jeffqchen/PS2EasyHDD/GameStar/3D Printing/Outer Shell & Tray Cover/Thin/Inner Tray Cover 9.5mm.stl

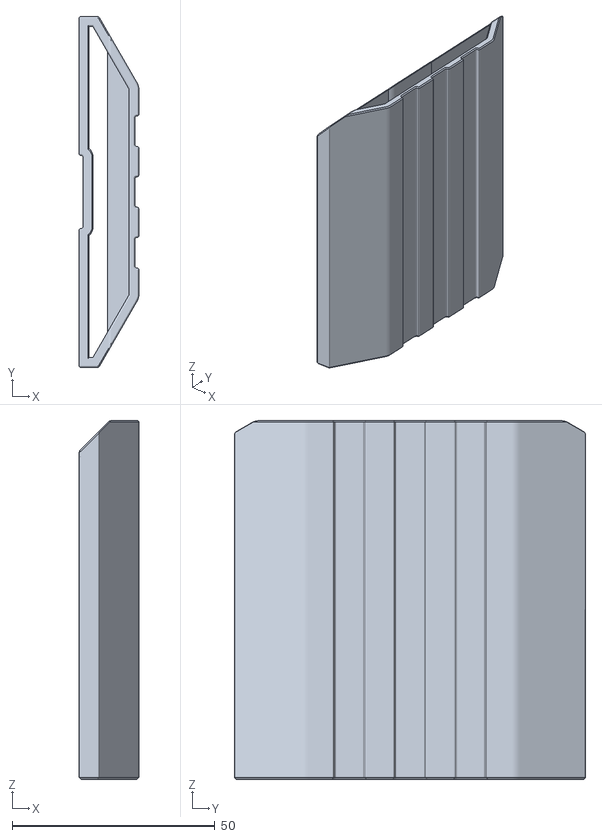
[picture p17: CAD file, 2024-02-22]
GameStar/3D Printing/Outer Shell & Tray Cover/Thin/Inner Tray Cover 9.5mm.stl
14.8 x 86.6 x 88.6
