jeffqchen/PS2EasyHDD/SCPH-10281/3D Printing/Inner Tray Short.stl

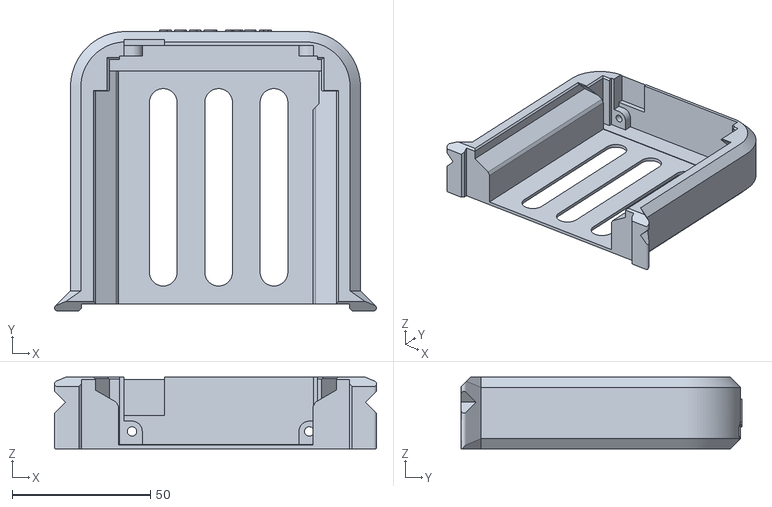
[picture p18: CAD file, 2024-02-20]
SCPH-10281/3D Printing/Inner Tray Short.stl
116.3 x 101.4 x 26.0
