jeffqchen/PS2EasyHDD/SCPH-10281/3D Printing/Outer Shell & Tray Cover/Inner Tray Cover 7mm.stl

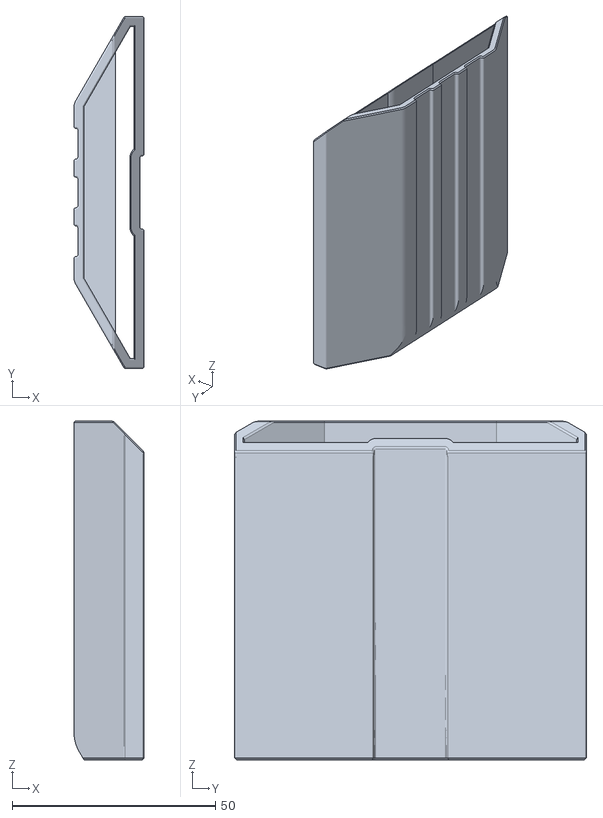
[picture p19: CAD file, 2024-02-18]
SCPH-10281/3D Printing/Outer Shell & Tray Cover/Inner Tray Cover 7mm.stl
17.3 x 86.6 x 83.4
