jeffqchen/PS2EasyHDD/GameStar/3D Printing/Inner Tray Short.stl

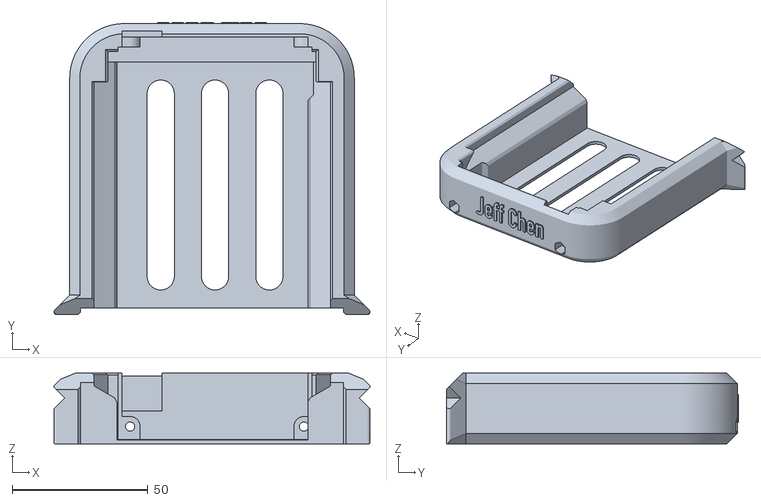
[picture p20: CAD file, 2024-02-22]
GameStar/3D Printing/Inner Tray Short.stl
116.3 x 107.7 x 26.0
