jeffqchen/PS2EasyHDD/GameStar/3D Printing/Outer Shell & Tray Cover/Thick/Inner Tray Cover 15mm.stl

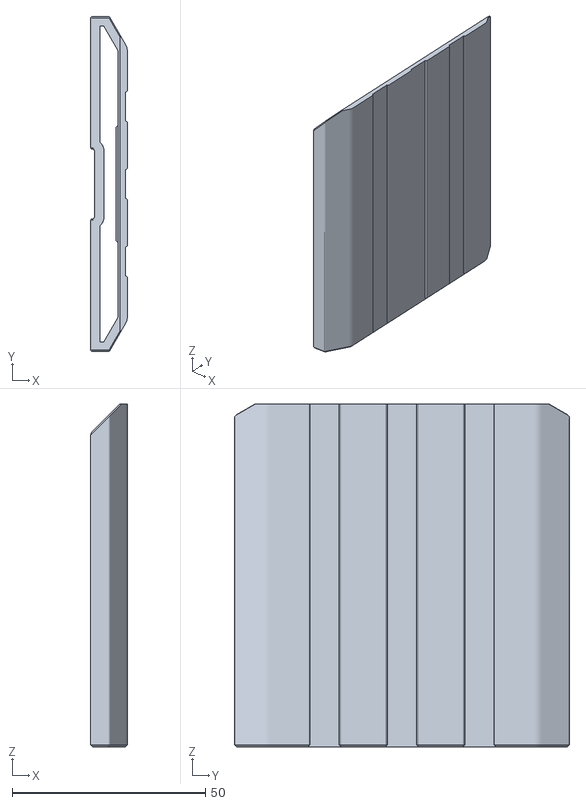
[picture p21: CAD file, 2024-02-22]
GameStar/3D Printing/Outer Shell & Tray Cover/Thick/Inner Tray Cover 15mm.stl
9.55 x 86.6 x 88.6
