jeffqchen/PS2EasyHDD/GameStar/3D Printing/Outer Shell & Tray Cover/Thin/Inner Tray Cover 7mm.stl

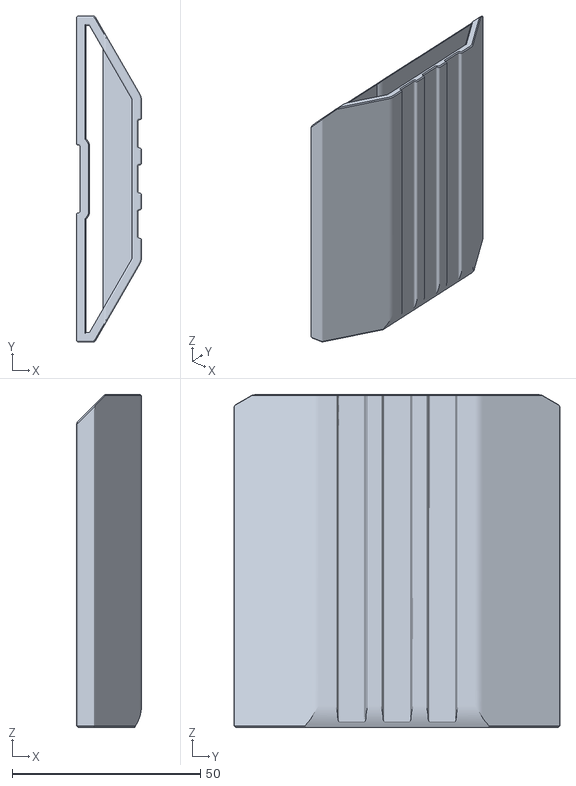
[picture p22: CAD file, 2024-02-22]
GameStar/3D Printing/Outer Shell & Tray Cover/Thin/Inner Tray Cover 7mm.stl
17.3 x 86.6 x 88.6
