jeffqchen/PS2EasyHDD/SCPH-10281/3D Printing/AIO for SCPH-10281.stl

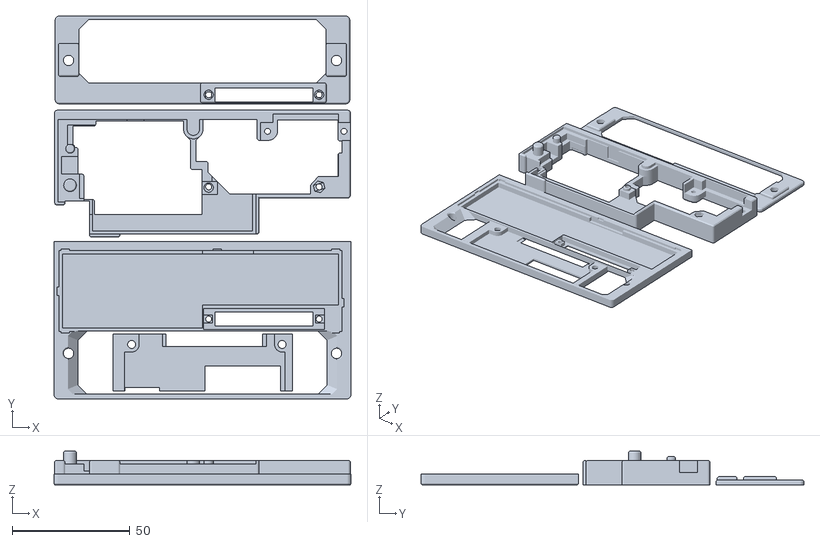
[picture p23: CAD file, 2024-02-19]
SCPH-10281/3D Printing/AIO for SCPH-10281.stl
126.4 x 163.0 x 14.4
