jeffqchen/PS2EasyHDD/SCPH-10281/3D Printing/Models Included In AIO/Mid Frame.stl

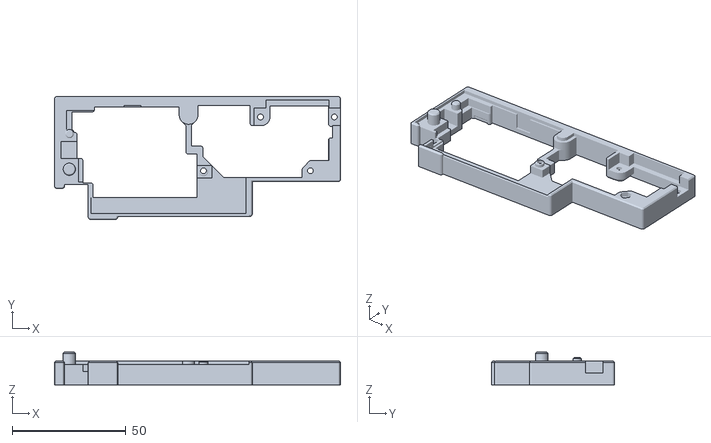
[picture p24: CAD file, 2024-02-19]
SCPH-10281/3D Printing/Models Included In AIO/Mid Frame.stl
125.8 x 54.0 x 14.4
