jeffqchen/PS2EasyHDD/SCPH-10281/3D Printing/Outer Shell & Tray Cover/Inner Tray Cover 9.5mm.stl

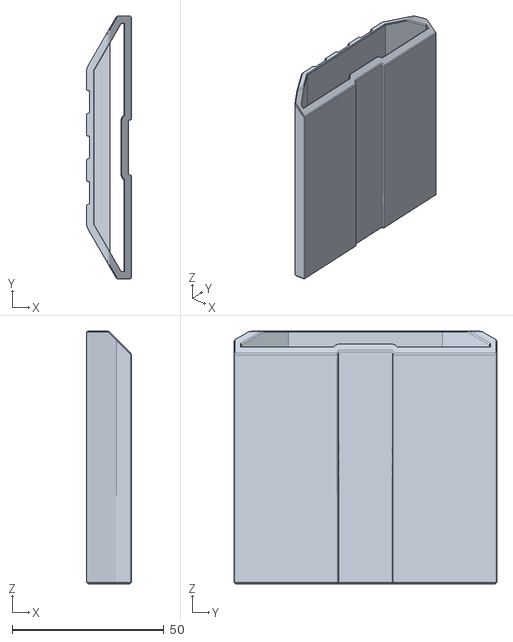
[picture p25: CAD file, 2024-02-18]
SCPH-10281/3D Printing/Outer Shell & Tray Cover/Inner Tray Cover 9.5mm.stl
14.8 x 86.6 x 83.4
