jeffqchen/PS2EasyHDD/SCPH-10350/3D Printing/Outer Shell & Tray Cover/Thick/Inner Tray Cover 12.5mm.stl

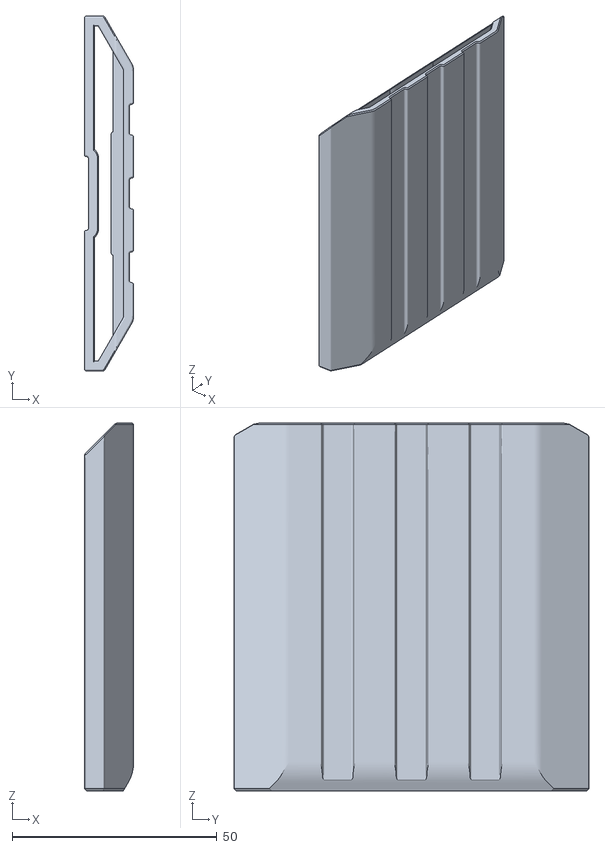
[picture p26: CAD file, 2024-02-19]
SCPH-10350/3D Printing/Outer Shell & Tray Cover/Thick/Inner Tray Cover 12.5mm.stl
12.0 x 86.6 x 89.7
