jeffqchen/PS2EasyHDD/SCPH-10350/3D Printing/Outer Shell & Tray Cover/Thin/Inner Tray Cover 9.5mm.stl

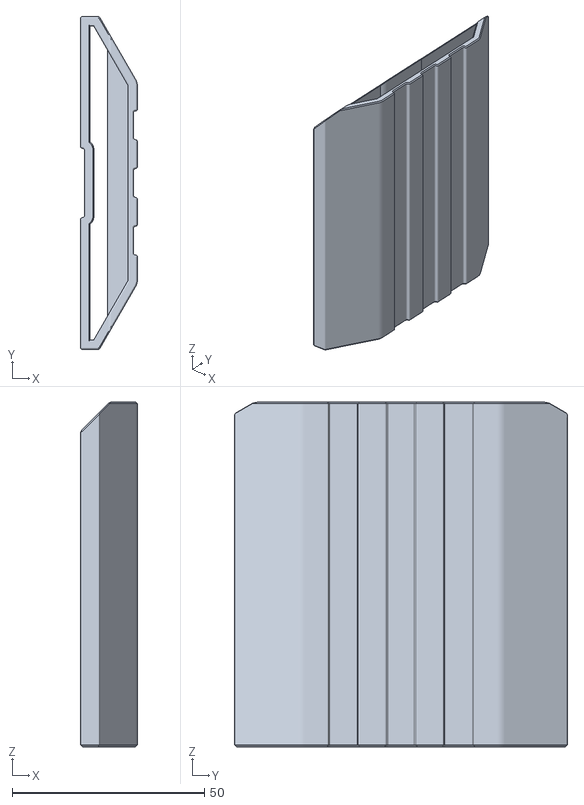
[picture p27: CAD file, 2024-02-19]
SCPH-10350/3D Printing/Outer Shell & Tray Cover/Thin/Inner Tray Cover 9.5mm.stl
14.8 x 86.6 x 89.7
