jeffqchen/PS2EasyHDD/GameStar/3D Printing/Models Included In AIO/Inner Spacer.stl

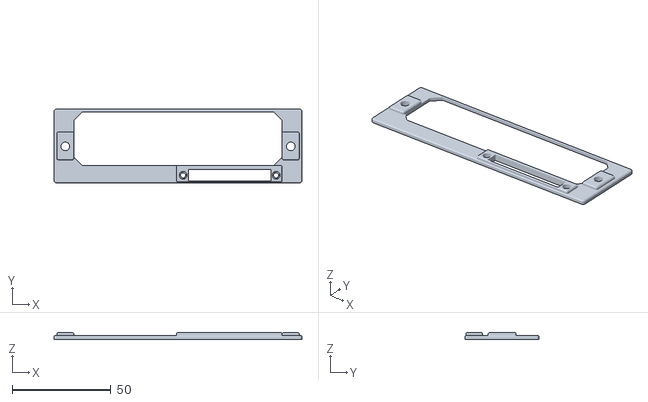
[picture p28: CAD file, 2024-02-19]
GameStar/3D Printing/Models Included In AIO/Inner Spacer.stl
125.4 x 37.4 x 3.50
