jeffqchen/PS2EasyHDD/SCPH-10281/3D Printing/Modem Board Cover.stl

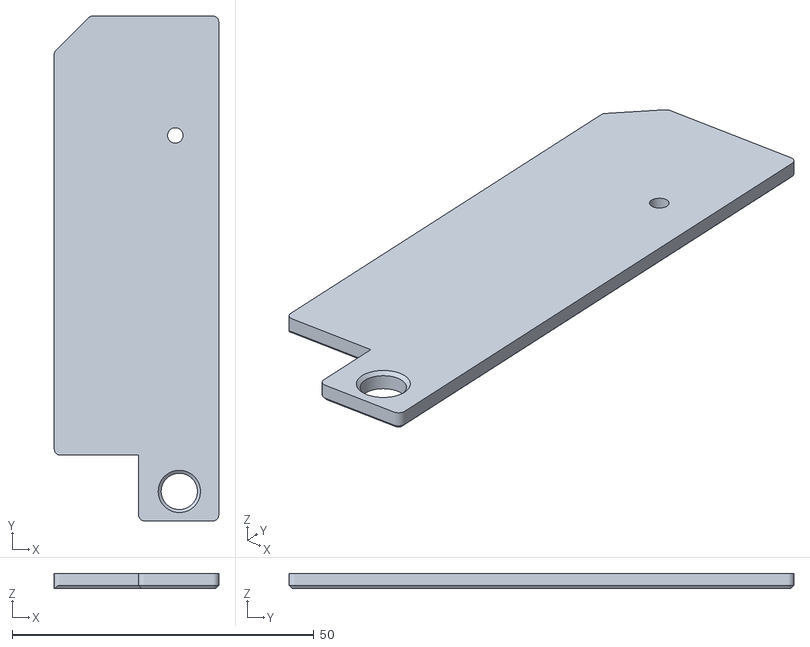
[picture p29: CAD file, 2024-02-18]
SCPH-10281/3D Printing/Modem Board Cover.stl
27.3 x 83.7 x 2.45
