jeffqchen/PS2EasyHDD/SCPH-10350/3D Printing/Outer Shell & Tray Cover/Thick/Inner Tray Cover 15mm.stl

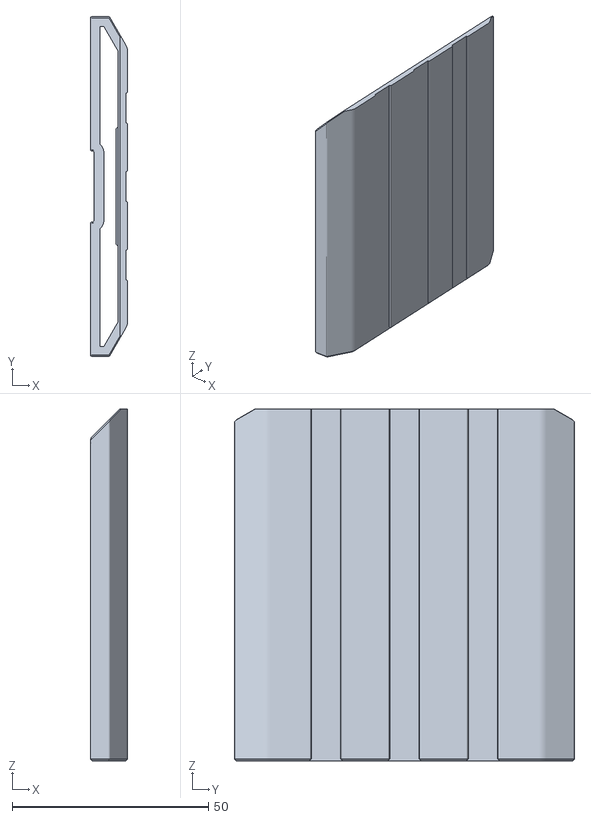
[picture p30: CAD file, 2024-02-19]
SCPH-10350/3D Printing/Outer Shell & Tray Cover/Thick/Inner Tray Cover 15mm.stl
9.55 x 86.6 x 89.7
