jeffqchen/PS2EasyHDD/SCPH-10350/3D Printing/Outer Shell & Tray Cover/Thin/Inner Tray Cover 7mm.stl

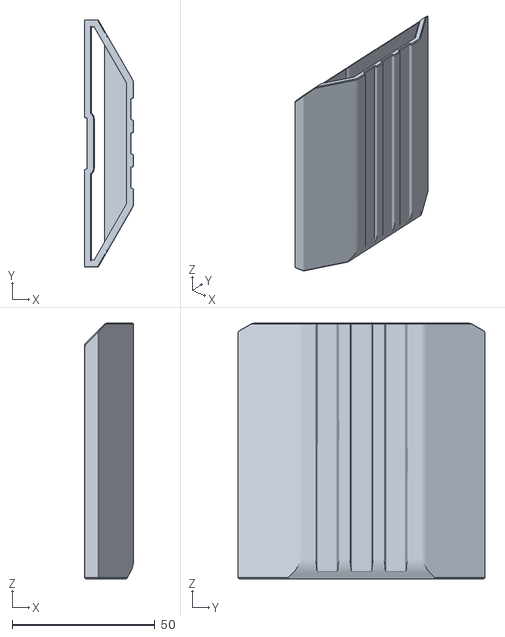
[picture p31: CAD file, 2024-02-19]
SCPH-10350/3D Printing/Outer Shell & Tray Cover/Thin/Inner Tray Cover 7mm.stl
17.3 x 86.6 x 89.7
